Trasselfrisyr/NuEVI/hardware/bcbreakout/mpxprevpic.png

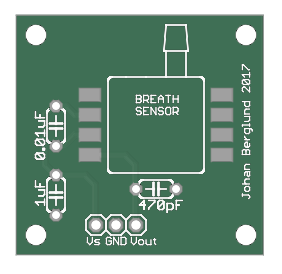
hardware/bcbreakout/mpxprevpic.png
