Trasselfrisyr/NuEVI/hardware/bitesensor/bitesensor02.jpg

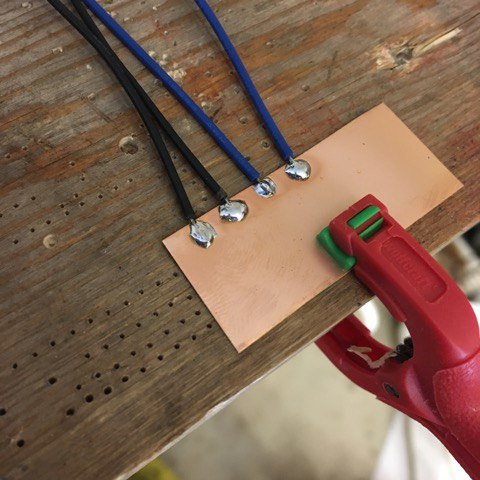
hardware/bitesensor/bitesensor02.jpg
