Trasselfrisyr/NuEVI/hardware/bitesensor/bitesensor06.jpg

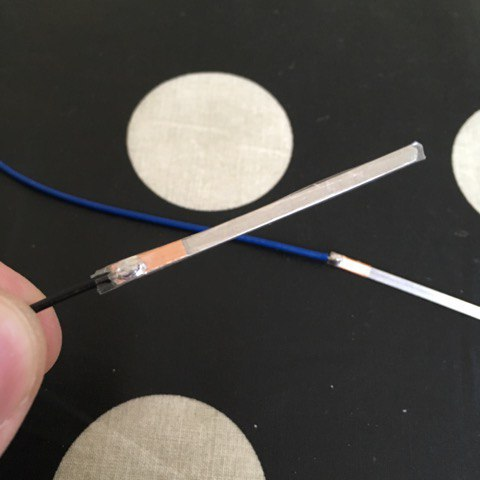
hardware/bitesensor/bitesensor06.jpg
