Trasselfrisyr/NuEVI/hardware/bitesensor/bitesensor07.jpg

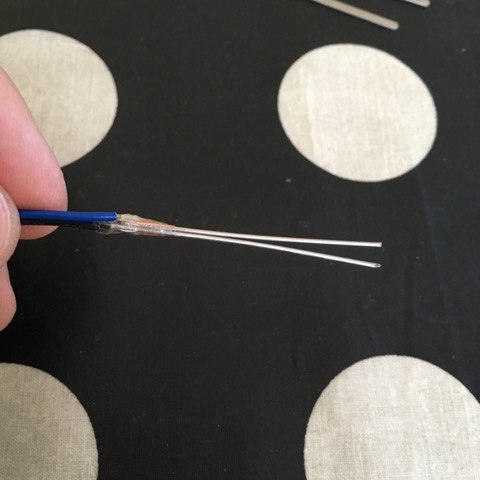
hardware/bitesensor/bitesensor07.jpg
