Trasselfrisyr/NuEVI/hardware/devboard/devboardpic.png

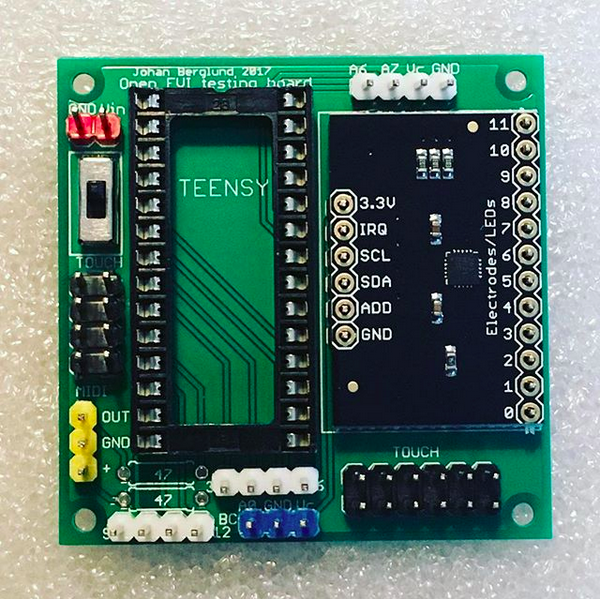
hardware/devboard/devboardpic.png
