Trasselfrisyr/NuEVI/simulation/include/core_pins.h

/* Teensyduino Core Library
 * http://www.pjrc.com/teensy/
 * Copyright (c) 2017 PJRC.COM, LLC.
 *
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
 * 2. If the Software is incorporated into a build system that allows
 * selection among a list of target devices, then similar target
 * devices manufactured by PJRC.COM must be included in the list of
 * target devices and selectable in the same manner.
 *
 * THE SOFTWARE IS PROVIDED "AS IS", WITHOUT WARRANTY OF ANY KIND,
 * EXPRESS OR IMPLIED, INCLUDING BUT NOT LIMITED TO THE WARRANTIES OF
 * MERCHANTABILITY, FITNESS FOR A PARTICULAR PURPOSE AND
 * NONINFRINGEMENT. IN NO EVENT SHALL THE AUTHORS OR COPYRIGHT HOLDERS
 * BE LIABLE FOR ANY CLAIM, DAMAGES OR OTHER LIABILITY, WHETHER IN AN
 * ACTION OF CONTRACT, TORT OR OTHERWISE, ARISING FROM, OUT OF OR IN
 * CONNECTION WITH THE SOFTWARE OR THE USE OR OTHER DEALINGS IN THE
 * SOFTWARE.
 */

#ifndef _core_pins_h_
#define _core_pins_h_

// #include "kinetis.h"
#include "pins_arduino.h"

#define HIGH		1
#define LOW		0
#define INPUT		0
#define OUTPUT		1
#define INPUT_PULLUP	2
#define INPUT_PULLDOWN   3
#define OUTPUT_OPENDRAIN 4
#define INPUT_DISABLE   5
#define LSBFIRST	0
#define MSBFIRST	1

#ifndef _BV
#define _BV(n)		(1<<(n))
#endif

#define CHANGE		4
#define FALLING		2
#define RISING		3

// Pin				Arduino
//  0	B16			RXD
//  1	B17			TXD
//  2	D0
//  3	A12	FTM1_CH0
//  4	A13	FTM1_CH1
//  5	D7	FTM0_CH7	OC0B/T1
//  6	D4	FTM0_CH4	OC0A
//  7	D2
//  8	D3			ICP1
//  9	C3	FTM0_CH2	OC1A
// 10	C4	FTM0_CH3	SS/OC1B
// 11	C6			MOSI/OC2A
// 12	C7			MISO
// 13	C5			SCK
// 14	D1
// 15	C0
// 16	B0	(FTM1_CH0)
// 17	B1	(FTM1_CH1)
// 18	B3			SDA
// 19	B2			SCL
// 20	D5	FTM0_CH5
// 21	D6	FTM0_CH6
// 22	C1	FTM0_CH0
// 23	C2	FTM0_CH1
// 24	A5	(FTM0_CH2)
// 25	B19
// 26	E1
// 27	C9
// 28	C8
// 29	C10
// 30	C11
// 31	E0
// 32	B18
// 33	A4	(FTM0_CH1)
// (34)	analog only
// (35)	analog only
// (36)	analog only
// (37)	analog only

// not available to user:
//	A0	FTM0_CH5	SWD Clock
//	A1	FTM0_CH6	USB ID
//	A2	FTM0_CH7	SWD Trace
//	A3	FTM0_CH0	SWD Data

#if defined(__MK20DX128__)
#define CORE_NUM_TOTAL_PINS     34
#define CORE_NUM_DIGITAL        34
#define CORE_NUM_INTERRUPT      34
#define CORE_NUM_ANALOG         14
#define CORE_NUM_PWM            10
#elif defined(__MK20DX256__)
#define CORE_NUM_TOTAL_PINS     34
#define CORE_NUM_DIGITAL        34
#define CORE_NUM_INTERRUPT      34
#define CORE_NUM_ANALOG         21
#define CORE_NUM_PWM            12
#elif defined(__MKL26Z64__)
#define CORE_NUM_TOTAL_PINS     27
#define CORE_NUM_DIGITAL        27
#define CORE_NUM_INTERRUPT      24  // really only 18, but 6 "holes"
#define CORE_NUM_ANALOG         13
#define CORE_NUM_PWM            10
#elif defined(__MK64FX512__)
#define CORE_NUM_TOTAL_PINS     64
#define CORE_NUM_DIGITAL        64
#define CORE_NUM_INTERRUPT      64
#define CORE_NUM_ANALOG         27
#define CORE_NUM_PWM            20
#elif defined(__MK66FX1M0__)
#define CORE_NUM_TOTAL_PINS     64
#define CORE_NUM_DIGITAL        64
#define CORE_NUM_INTERRUPT      64
#define CORE_NUM_ANALOG         25
#define CORE_NUM_PWM            22
#endif

// These MAX_PIN_PORTx values have the highest Kinetis pin index
// that is used for a given port.
#if defined(__MK20DX128__) || defined(__MK20DX256__)
#define CORE_MAX_PIN_PORTA        13
#define CORE_MAX_PIN_PORTB        19
#define CORE_MAX_PIN_PORTC        11
#define CORE_MAX_PIN_PORTD         7
#define CORE_MAX_PIN_PORTE         1
#elif defined(__MKL26Z64__)
#define CORE_MAX_PIN_PORTA         2
#define CORE_MAX_PIN_PORTB        17
#define CORE_MAX_PIN_PORTC         7
#define CORE_MAX_PIN_PORTD         7
#define CORE_MAX_PIN_PORTE        30
#elif defined(__MK64FX512__) || defined(__MK66FX1M0__)
#define CORE_MAX_PIN_PORTA        29
#define CORE_MAX_PIN_PORTB        23
#define CORE_MAX_PIN_PORTC        11
#define CORE_MAX_PIN_PORTD        15
#define CORE_MAX_PIN_PORTE        26
#endif


#if defined(__MK20DX128__) || defined(__MK20DX256__)

#define CORE_PIN0_BIT		16
#define CORE_PIN1_BIT		17
#define CORE_PIN2_BIT		0
#define CORE_PIN3_BIT		12
#define CORE_PIN4_BIT		13
#define CORE_PIN5_BIT		7
#define CORE_PIN6_BIT		4
#define CORE_PIN7_BIT		2
#define CORE_PIN8_BIT		3
#define CORE_PIN9_BIT		3
#define CORE_PIN10_BIT		4
#define CORE_PIN11_BIT		6
#define CORE_PIN12_BIT		7
#define CORE_PIN13_BIT		5
#define CORE_PIN14_BIT		1
#define CORE_PIN15_BIT		0
#define CORE_PIN16_BIT		0
#define CORE_PIN17_BIT		1
#define CORE_PIN18_BIT		3
#define CORE_PIN19_BIT		2
#define CORE_PIN20_BIT		5
#define CORE_PIN21_BIT		6
#define CORE_PIN22_BIT		1
#define CORE_PIN23_BIT		2
#define CORE_PIN24_BIT		5
#define CORE_PIN25_BIT		19
#define CORE_PIN26_BIT		1
#define CORE_PIN27_BIT		9
#define CORE_PIN28_BIT		8
#define CORE_PIN29_BIT		10
#define CORE_PIN30_BIT		11
#define CORE_PIN31_BIT		0
#define CORE_PIN32_BIT		18
#define CORE_PIN33_BIT		4

#define CORE_PIN0_BITMASK	(1<<(CORE_PIN0_BIT))
#define CORE_PIN1_BITMASK	(1<<(CORE_PIN1_BIT))
#define CORE_PIN2_BITMASK	(1<<(CORE_PIN2_BIT))
#define CORE_PIN3_BITMASK	(1<<(CORE_PIN3_BIT))
#define CORE_PIN4_BITMASK	(1<<(CORE_PIN4_BIT))
#define CORE_PIN5_BITMASK	(1<<(CORE_PIN5_BIT))
#define CORE_PIN6_BITMASK	(1<<(CORE_PIN6_BIT))
#define CORE_PIN7_BITMASK	(1<<(CORE_PIN7_BIT))
#define CORE_PIN8_BITMASK	(1<<(CORE_PIN8_BIT))
#define CORE_PIN9_BITMASK	(1<<(CORE_PIN9_BIT))
#define CORE_PIN10_BITMASK	(1<<(CORE_PIN10_BIT))
#define CORE_PIN11_BITMASK	(1<<(CORE_PIN11_BIT))
#define CORE_PIN12_BITMASK	(1<<(CORE_PIN12_BIT))
#define CORE_PIN13_BITMASK	(1<<(CORE_PIN13_BIT))
#define CORE_PIN14_BITMASK	(1<<(CORE_PIN14_BIT))
#define CORE_PIN15_BITMASK	(1<<(CORE_PIN15_BIT))
#define CORE_PIN16_BITMASK	(1<<(CORE_PIN16_BIT))
#define CORE_PIN17_BITMASK	(1<<(CORE_PIN17_BIT))
#define CORE_PIN18_BITMASK	(1<<(CORE_PIN18_BIT))
#define CORE_PIN19_BITMASK	(1<<(CORE_PIN19_BIT))
#define CORE_PIN20_BITMASK	(1<<(CORE_PIN20_BIT))
#define CORE_PIN21_BITMASK	(1<<(CORE_PIN21_BIT))
#define CORE_PIN22_BITMASK	(1<<(CORE_PIN22_BIT))
#define CORE_PIN23_BITMASK	(1<<(CORE_PIN23_BIT))
#define CORE_PIN24_BITMASK	(1<<(CORE_PIN24_BIT))
#define CORE_PIN25_BITMASK	(1<<(CORE_PIN25_BIT))
#define CORE_PIN26_BITMASK	(1<<(CORE_PIN26_BIT))
#define CORE_PIN27_BITMASK	(1<<(CORE_PIN27_BIT))
#define CORE_PIN28_BITMASK	(1<<(CORE_PIN28_BIT))
#define CORE_PIN29_BITMASK	(1<<(CORE_PIN29_BIT))
#define CORE_PIN30_BITMASK	(1<<(CORE_PIN30_BIT))
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
// 		  else if (pin == 27) {
// 			return (CORE_PIN27_PINREG & CORE_PIN27_BITMASK) ? 1 : 0;
// 		} else if (pin == 28) {
// 			return (CORE_PIN28_PINREG & CORE_PIN28_BITMASK) ? 1 : 0;
// 		} else if (pin == 29) {
// 			return (CORE_PIN29_PINREG & CORE_PIN29_BITMASK) ? 1 : 0;
// 		} else if (pin == 30) {
// 			return (CORE_PIN30_PINREG & CORE_PIN30_BITMASK) ? 1 : 0;
// 		} else if (pin == 31) {
// 			return (CORE_PIN31_PINREG & CORE_PIN31_BITMASK) ? 1 : 0;
// 		} else if (pin == 32) {
// 			return (CORE_PIN32_PINREG & CORE_PIN32_BITMASK) ? 1 : 0;
// 		} else if (pin == 33) {
// 			return (CORE_PIN33_PINREG & CORE_PIN33_BITMASK) ? 1 : 0;
// 		}
// 		#endif
// 		#if defined(CORE_PIN34_PINREG)
// 		  else if (pin == 34) {
// 			return (CORE_PIN34_PINREG & CORE_PIN34_BITMASK) ? 1 : 0;
// 		} else if (pin == 35) {
// 			return (CORE_PIN35_PINREG & CORE_PIN35_BITMASK) ? 1 : 0;
// 		} else if (pin == 36) {
// 			return (CORE_PIN36_PINREG & CORE_PIN36_BITMASK) ? 1 : 0;
// 		} else if (pin == 37) {
// 			return (CORE_PIN37_PINREG & CORE_PIN37_BITMASK) ? 1 : 0;
// 		} else if (pin == 38) {
// 			return (CORE_PIN38_PINREG & CORE_PIN38_BITMASK) ? 1 : 0;
// 		} else if (pin == 39) {
// 			return (CORE_PIN39_PINREG & CORE_PIN39_BITMASK) ? 1 : 0;
// 		} else if (pin == 40) {
// 			return (CORE_PIN40_PINREG & CORE_PIN40_BITMASK) ? 1 : 0;
// 		} else if (pin == 41) {
// 			return (CORE_PIN41_PINREG & CORE_PIN41_BITMASK) ? 1 : 0;
// 		} else if (pin == 42) {
// 			return (CORE_PIN42_PINREG & CORE_PIN42_BITMASK) ? 1 : 0;
// 		} else if (pin == 43) {
// 			return (CORE_PIN43_PINREG & CORE_PIN43_BITMASK) ? 1 : 0;
// 		} else if (pin == 44) {
// 			return (CORE_PIN44_PINREG & CORE_PIN44_BITMASK) ? 1 : 0;
// 		} else if (pin == 45) {
// 			return (CORE_PIN45_PINREG & CORE_PIN45_BITMASK) ? 1 : 0;
// 		} else if (pin == 46) {
// 			return (CORE_PIN46_PINREG & CORE_PIN46_BITMASK) ? 1 : 0;
// 		} else if (pin == 47) {
// 			return (CORE_PIN47_PINREG & CORE_PIN47_BITMASK) ? 1 : 0;
// 		} else if (pin == 48) {
// 			return (CORE_PIN48_PINREG & CORE_PIN48_BITMASK) ? 1 : 0;
// 		} else if (pin == 49) {
// 			return (CORE_PIN49_PINREG & CORE_PIN49_BITMASK) ? 1 : 0;
// 		} else if (pin == 50) {
// 			return (CORE_PIN50_PINREG & CORE_PIN50_BITMASK) ? 1 : 0;
// 		} else if (pin == 51) {
// 			return (CORE_PIN51_PINREG & CORE_PIN51_BITMASK) ? 1 : 0;
// 		} else if (pin == 52) {
// 			return (CORE_PIN52_PINREG & CORE_PIN52_BITMASK) ? 1 : 0;
// 		} else if (pin == 53) {
// 			return (CORE_PIN53_PINREG & CORE_PIN53_BITMASK) ? 1 : 0;
// 		} else if (pin == 54) {
// 			return (CORE_PIN54_PINREG & CORE_PIN54_BITMASK) ? 1 : 0;
// 		} else if (pin == 55) {
// 			return (CORE_PIN55_PINREG & CORE_PIN55_BITMASK) ? 1 : 0;
// 		} else if (pin == 56) {
// 			return (CORE_PIN56_PINREG & CORE_PIN56_BITMASK) ? 1 : 0;
// 		} else if (pin == 57) {
// 			return (CORE_PIN57_PINREG & CORE_PIN57_BITMASK) ? 1 : 0;
// 		} else if (pin == 58) {
// 			return (CORE_PIN58_PINREG & CORE_PIN58_BITMASK) ? 1 : 0;
// 		} else if (pin == 59) {
// 			return (CORE_PIN59_PINREG & CORE_PIN59_BITMASK) ? 1 : 0;
// 		} else if (pin == 60) {
// 			return (CORE_PIN60_PINREG & CORE_PIN60_BITMASK) ? 1 : 0;
// 		} else if (pin == 61) {
// 			return (CORE_PIN61_PINREG & CORE_PIN61_BITMASK) ? 1 : 0;
// 		} else if (pin == 62) {
// 			return (CORE_PIN62_PINREG & CORE_PIN62_BITMASK) ? 1 : 0;
// 		} else if (pin == 63) {
// 			return (CORE_PIN63_PINREG & CORE_PIN63_BITMASK) ? 1 : 0;
// 		}
// 		#endif
// 		  else {
// 			return 0;
// 		}
// 	} else {
// 		#if defined(KINETISK)
// 		return *portInputRegister(pin);
// 		#else
// 		return (*portInputRegister(pin) & digitalPinToBitMask(pin)) ? 1 : 0;
// 		#endif
// 	}
// }


void pinMode(uint8_t pin, uint8_t mode);
void init_pins(void);
void analogWrite(uint8_t pin, int val);

uint32_t analogWriteRes(uint32_t bits);
static inline uint32_t analogWriteResolution(uint32_t bits) { return analogWriteRes(bits); }
void analogWriteFrequency(uint8_t pin, float frequency);
// void analogWriteDAC0(int val);
// void analogWriteDAC1(int val);
// #ifdef __cplusplus
// void attachInterruptVector(IRQ_NUMBER_t irq, void (*function)(void));
// #else
// void attachInterruptVector(enum IRQ_NUMBER_t irq, void (*function)(void));
// #endif
// void attachInterrupt(uint8_t pin, void (*function)(void), int mode);
// void detachInterrupt(uint8_t pin);
// void _init_Teensyduino_internal_(void);

int analogRead(uint8_t pin);
void analogReference(uint8_t type);
void analogReadRes(unsigned int bits);
static inline void analogReadResolution(unsigned int bits) { analogReadRes(bits); }
void analogReadAveraging(unsigned int num);
void analog_init(void);


#if defined(__MK20DX128__) || defined(__MK20DX256__) || defined(__MK64FX512__) || defined(__MK66FX1M0__)
#define DEFAULT         0
#define INTERNAL        2
#define INTERNAL1V2     2
#define INTERNAL1V1     2
#define EXTERNAL        0

#elif defined(__MKL26Z64__)
#define DEFAULT         0
#define INTERNAL        0
#define EXTERNAL        1
#endif


int touchRead(uint8_t pin);


// static inline void shiftOut(uint8_t, uint8_t, uint8_t, uint8_t) __attribute__((always_inline, unused));
extern void _shiftOut(uint8_t dataPin, uint8_t clockPin, uint8_t bitOrder, uint8_t value) __attribute__((noinline));
extern void shiftOut_lsbFirst(uint8_t dataPin, uint8_t clockPin, uint8_t value) __attribute__((noinline));
extern void shiftOut_msbFirst(uint8_t dataPin, uint8_t clockPin, uint8_t value) __attribute__((noinline));

// static inline void shiftOut(uint8_t dataPin, uint8_t clockPin, uint8_t bitOrder, uint8_t value)
// {
//         if (__builtin_constant_p(bitOrder)) {
//                 if (bitOrder == LSBFIRST) {
//                         shiftOut_lsbFirst(dataPin, clockPin, value);
//                 } else {
//                         shiftOut_msbFirst(dataPin, clockPin, value);
//                 }
//         } else {
//                 _shiftOut(dataPin, clockPin, bitOrder, value);
//         }
// }

static inline uint8_t shiftIn(uint8_t, uint8_t, uint8_t) __attribute__((always_inline, unused));
extern uint8_t _shiftIn(uint8_t dataPin, uint8_t clockPin, uint8_t bitOrder) __attribute__((noinline));
extern uint8_t shiftIn_lsbFirst(uint8_t dataPin, uint8_t clockPin) __attribute__((noinline));
extern uint8_t shiftIn_msbFirst(uint8_t dataPin, uint8_t clockPin) __attribute__((noinline));

static inline uint8_t shiftIn(uint8_t dataPin, uint8_t clockPin, uint8_t bitOrder)
{
        if (__builtin_constant_p(bitOrder)) {
                if (bitOrder == LSBFIRST) {
                        return shiftIn_lsbFirst(dataPin, clockPin);
                } else {
                        return shiftIn_msbFirst(dataPin, clockPin);
                }
        } else {
                return _shiftIn(dataPin, clockPin, bitOrder);
        }
}

void _reboot_Teensyduino_(void);
void _restart_Teensyduino_(void);

void yield(void);

void delay(uint32_t msec);

// extern volatile uint32_t systick_millis_count;

// static inline uint32_t millis(void) __attribute__((always_inline, unused));
// static inline uint32_t millis(void)
// {
// 	// Reading a volatile variable to another volatile
// 	// seems redundant, but isn't for some cases.
// 	// Eventually this should probably be replaced by a
// 	// proper memory barrier or other technique.  Please
// 	// do not remove this "redundant" code without
// 	// carefully verifying the case mentioned here:
// 	//
// 	// https://forum.pjrc.com/threads/17469-millis%28%29-on-teensy-3?p=104924&viewfull=1#post104924
// 	//
// 	volatile uint32_t ret = systick_millis_count; // single aligned 32 bit is atomic
// 	return ret;
// }

// uint32_t micros(void);
/*
static inline void delayMicroseconds(uint32_t) __attribute__((always_inline, unused));
static inline void delayMicroseconds(uint32_t usec)
{
#if F_CPU == 256000000
	uint32_t n = usec * 85;
#elif F_CPU == 240000000
	uint32_t n = usec * 80;
#elif F_CPU == 216000000
	uint32_t n = usec * 72;
#elif F_CPU == 192000000
	uint32_t n = usec * 64;
#elif F_CPU == 180000000
	uint32_t n = usec * 60;
#elif F_CPU == 168000000
	uint32_t n = usec * 56;
#elif F_CPU == 144000000
	uint32_t n = usec * 48;
#elif F_CPU == 120000000
	uint32_t n = usec * 40;
#elif F_CPU == 96000000
	uint32_t n = usec << 5;
#elif F_CPU == 72000000
	uint32_t n = usec * 24;
#elif F_CPU == 48000000
	uint32_t n = usec << 4;
#elif F_CPU == 24000000
	uint32_t n = usec << 3;
#elif F_CPU == 16000000
	uint32_t n = usec << 2;
#elif F_CPU == 8000000
	uint32_t n = usec << 1;
#elif F_CPU == 4000000
	uint32_t n = usec;
#elif F_CPU == 2000000
	uint32_t n = usec >> 1;
#endif
    // changed because a delay of 1 micro Sec @ 2MHz will be 0
	if (n == 0) return;
	__asm__ volatile(
		"L_%=_delayMicroseconds:"		"\n\t"
#if F_CPU < 24000000
		"nop"					"\n\t"
#endif
#ifdef KINETISL
		"sub    %0, #1"				"\n\t"
		"bne    L_%=_delayMicroseconds"		"\n"
		: "+l" (n) :
#else
		"subs   %0, #1"				"\n\t"
		"bne    L_%=_delayMicroseconds"		"\n"
		: "+r" (n) :
#endif
	);
}
*/
#ifdef __cplusplus
}
#endif








#ifdef __cplusplus
extern "C" {
#endif
unsigned long rtc_get(void);
void rtc_set(unsigned long t);
void rtc_compensate(int adjust);
#ifdef __cplusplus
}
class teensy3_clock_class
{
public:
	static unsigned long get(void) __attribute__((always_inline)) { return rtc_get(); }
	static void set(unsigned long t) __attribute__((always_inline)) { rtc_set(t); }
	static void compensate(int adj) __attribute__((always_inline)) { rtc_compensate(adj); }
};
extern teensy3_clock_class Teensy3Clock;
#endif




#endif
